samanbeer/macropad_stasis/KiCAD_project/OPL_Kicad_Library-master/images/XIAO_Family_2.png

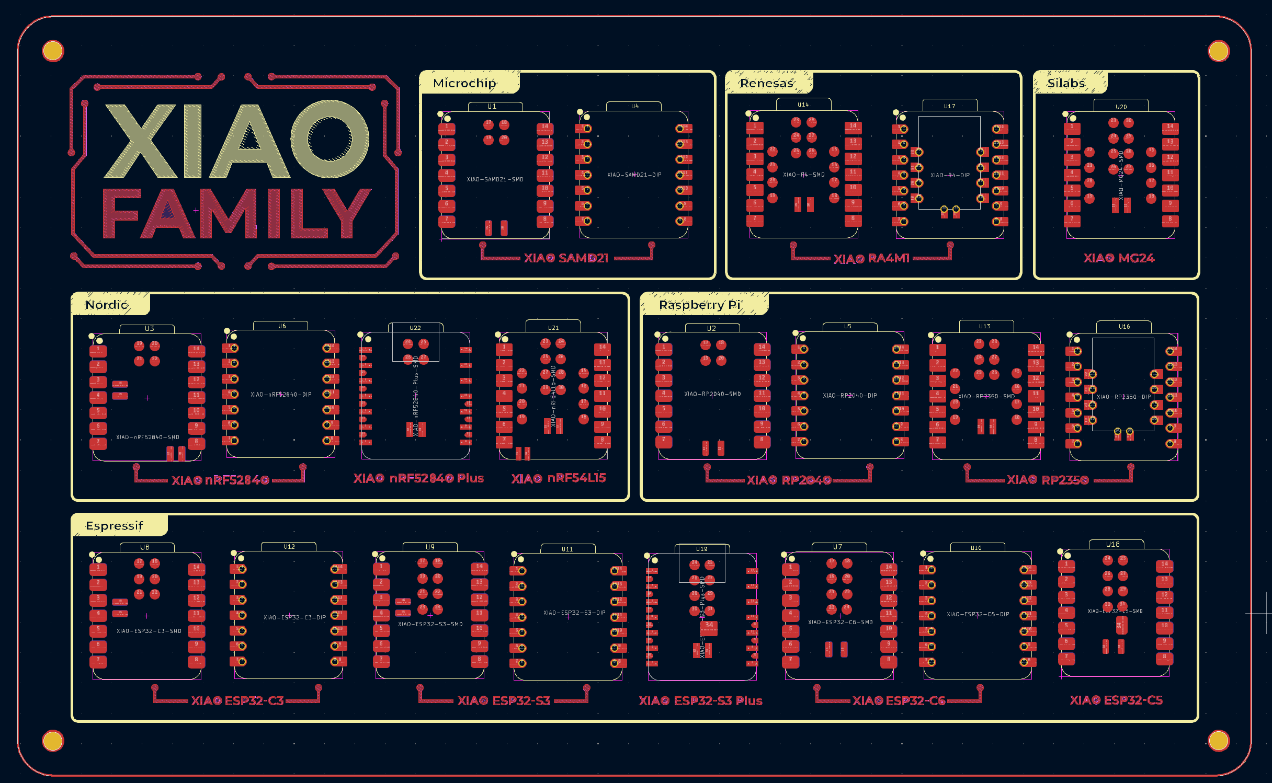
KiCAD_project/OPL_Kicad_Library-master/images/XIAO_Family_2.png
